nicmarquardt/airconstellations/AirConstellations STL Models (V3)/AirConstellation v3 - Three-Cable Clip.stl

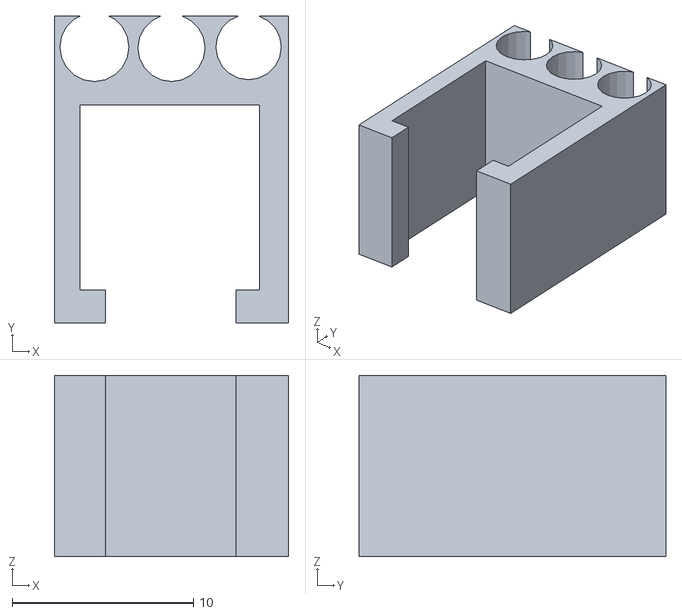
[picture p18: CAD file, 2021-10-11, an earlier design]
AirConstellations STL Models (V3)/AirConstellation v3 - Three-Cable Clip.stl
12.9 x 16.9 x 10.00
